leon-h-a/lampadine/pcb/v4/jlc parts images/01.png

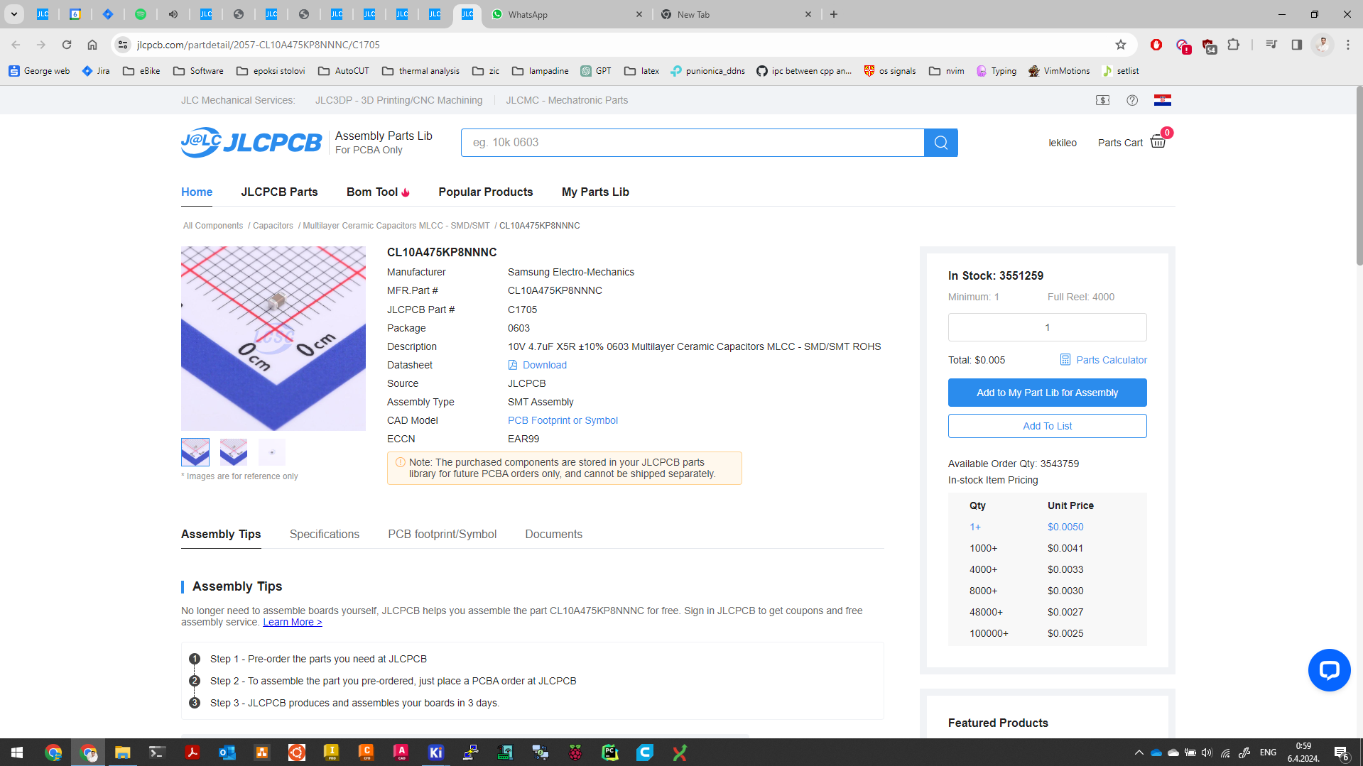
pcb/v4/jlc parts images/01.png
