leon-h-a/lampadine/pcb/v4/jlc parts images/02.png

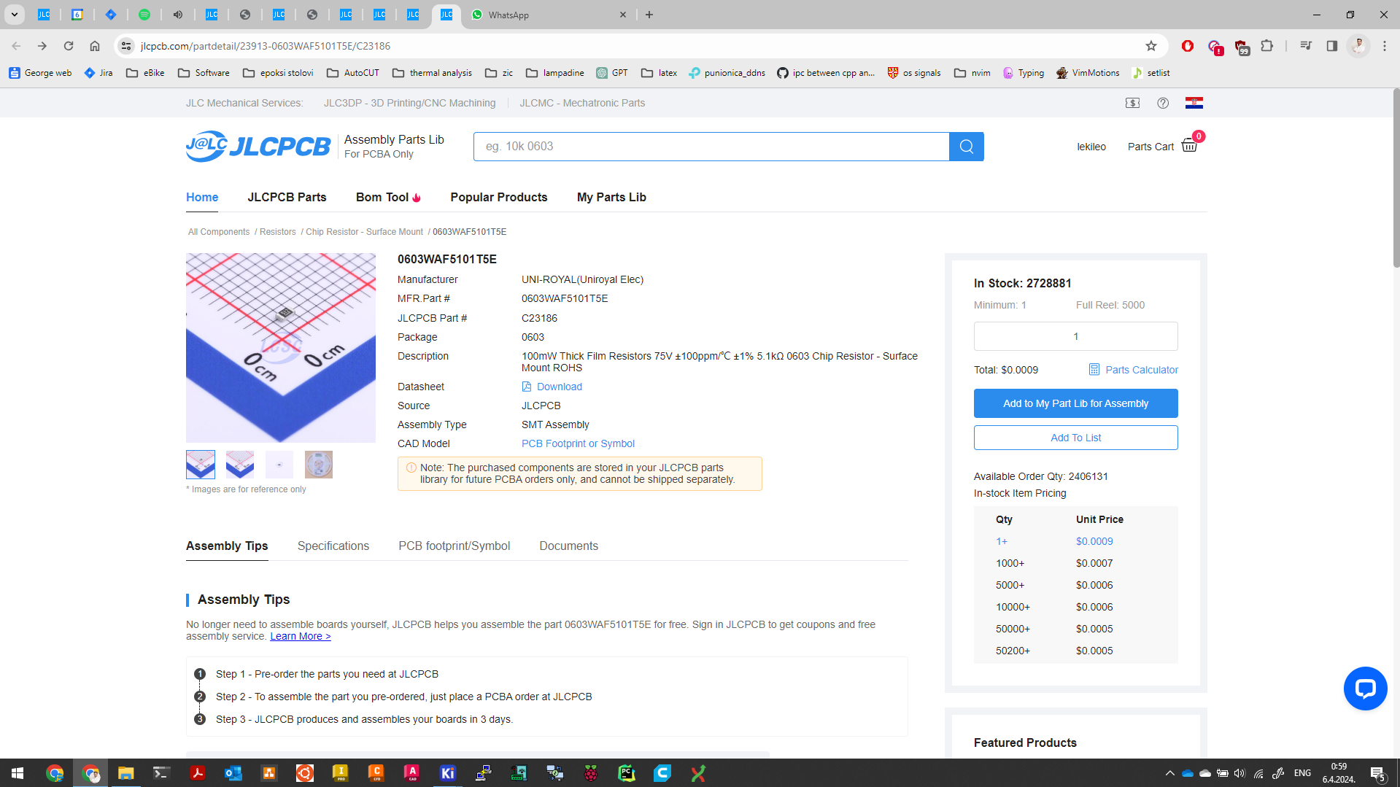
pcb/v4/jlc parts images/02.png
