leon-h-a/lampadine/pcb/v4/jlc parts images/06.png

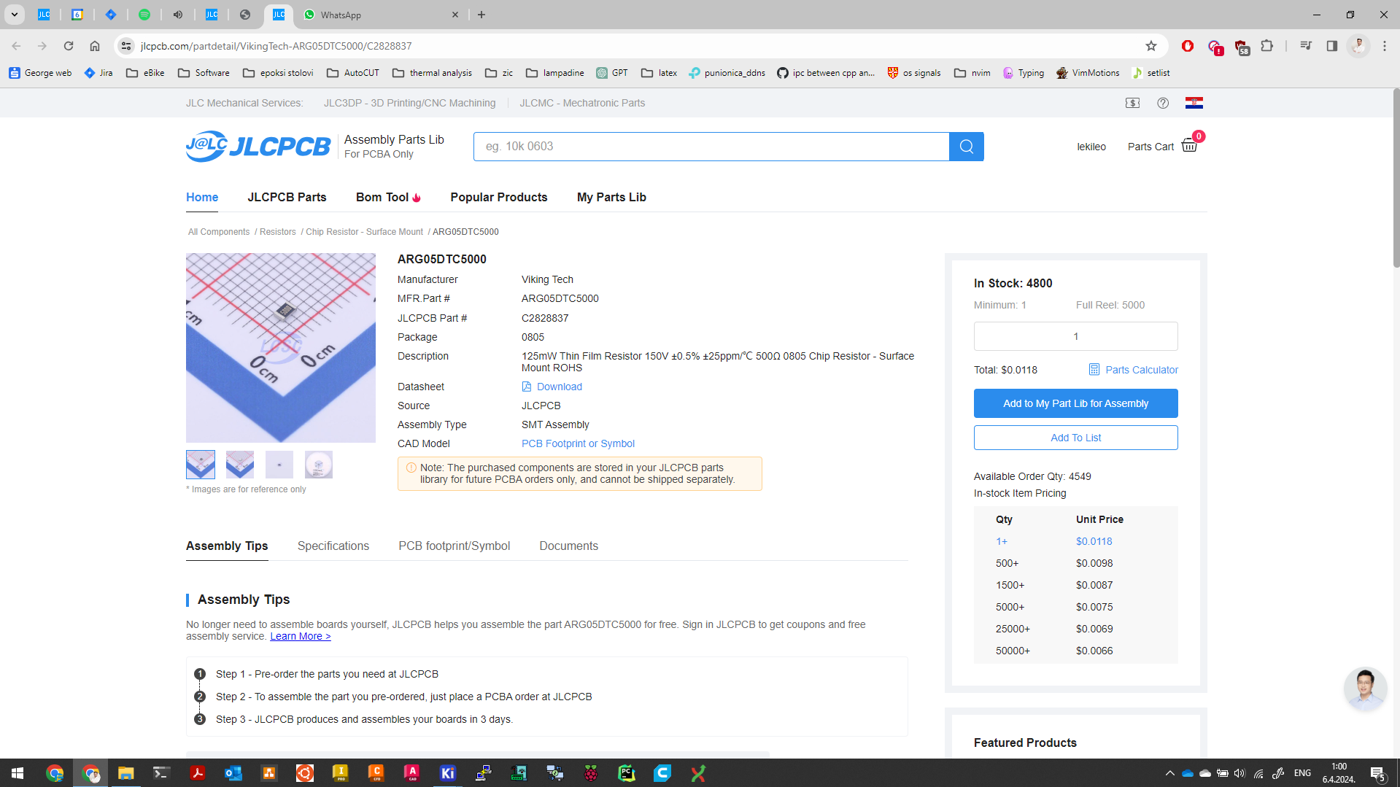
pcb/v4/jlc parts images/06.png
